ColbyDAllen/F-UVC-WaterBottle/Hardware/MCAD_v2/SolidWorks_Files/F-UVC-Solar_RevA1.1.3_FilterCartridge_COMBINE.SLDPRT

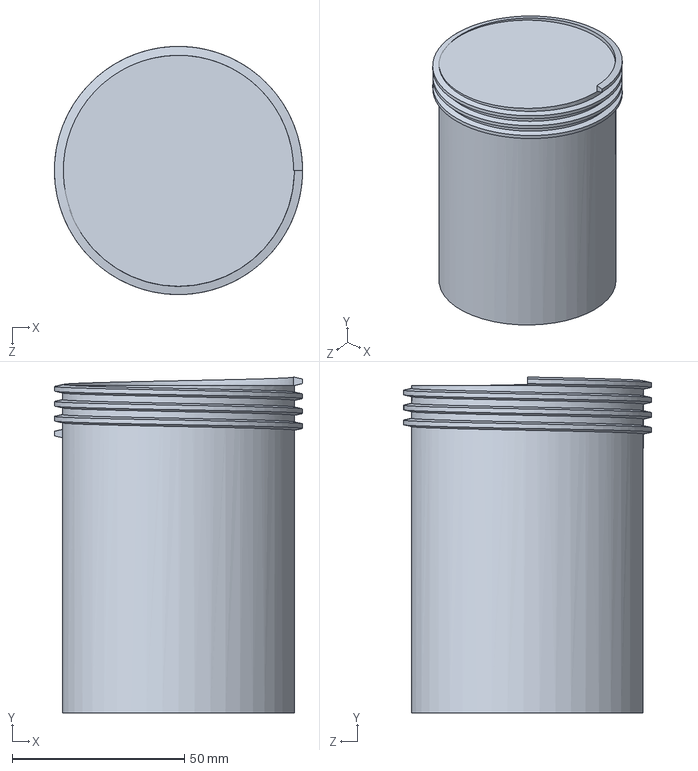
[picture p21: CAD file, 2025-12-21]
Hardware/MCAD_v2/SolidWorks_Files/F-UVC-Solar_RevA1.1.3_FilterCartridge_COMBINE.SLDPRT
72.0 x 97.5 x 72.0 mm
